raphatex/ESP-32-ruler/Arduino programs/esp32_OS/icons.h

/*
 * https://javl.github.io/image2cpp/
 */
// 'icons', 42x42px
const unsigned char icons[][252] PROGMEM = {
  { // tetris
  0x1f, 0xff, 0xff, 0xff, 0xfe, 0x00, 0x3f, 0xff, 0xff, 0xff, 0xff, 0x00, 0x70, 0x00, 0x00, 0x00, 
  0x03, 0x80, 0xe0, 0x00, 0x00, 0x00, 0x01, 0xc0, 0xc0, 0x00, 0x00, 0x00, 0x00, 0xc0, 0xc0, 0x00, 
  0x00, 0x00, 0x00, 0xc0, 0xc1, 0xff, 0xff, 0xff, 0xe0, 0xc0, 0xc1, 0x00, 0x80, 0x40, 0x20, 0xc0, 
  0xc1, 0x7e, 0xbf, 0x5f, 0xa0, 0xc0, 0xc1, 0x7e, 0xbf, 0x5f, 0xa0, 0xc0, 0xc1, 0x7e, 0xbf, 0x5f, 
  0xa0, 0xc0, 0xc1, 0x7e, 0xbf, 0x5f, 0xa0, 0xc0, 0xc1, 0x7e, 0xbf, 0x5f, 0xa0, 0xc0, 0xc1, 0x7e, 
  0xbf, 0x5f, 0xa0, 0xc0, 0xc1, 0x00, 0x80, 0x40, 0x20, 0xc0, 0xc1, 0xff, 0xff, 0xff, 0xe0, 0xc0, 
  0xc0, 0x00, 0x80, 0x40, 0x00, 0xc0, 0xc0, 0x00, 0xbf, 0x40, 0x00, 0xc0, 0xc0, 0x00, 0xbf, 0x40, 
  0x00, 0xc0, 0xc0, 0x00, 0xbf, 0x40, 0x00, 0xc0, 0xc0, 0x00, 0xbf, 0x40, 0x00, 0xc0, 0xc0, 0x00, 
  0xbf, 0x40, 0x00, 0xc0, 0xc0, 0x00, 0xbf, 0x40, 0x00, 0xc0, 0xc0, 0x00, 0x80, 0x40, 0x00, 0xc0, 
  0xc0, 0x00, 0xff, 0xc0, 0x00, 0xc0, 0xc0, 0x00, 0x00, 0x00, 0x00, 0xc0, 0xc0, 0x00, 0x00, 0x00, 
  0x00, 0xc0, 0xc0, 0x00, 0x00, 0x00, 0x00, 0xc0, 0xc0, 0x00, 0x00, 0x00, 0x00, 0xc0, 0xc3, 0xef, 
  0x7d, 0xe2, 0xf0, 0xc0, 0xc0, 0x88, 0x11, 0x10, 0x80, 0xc0, 0xc0, 0x88, 0x11, 0x12, 0x80, 0xc0, 
  0xc0, 0x8e, 0x11, 0xe2, 0xf0, 0xc0, 0xc0, 0x88, 0x11, 0x42, 0x10, 0xc0, 0xc0, 0x88, 0x11, 0x22, 
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
	0x20, 0xc0, 0xc0, 0xff, 0xe1, 0xff, 0xc0, 0xc0, 0xc0, 0x00, 0x00, 0x00, 0x00, 0xc0, 0xc0, 0x00, 
	0x00, 0x00, 0x00, 0xc0, 0xe0, 0x00, 0x00, 0x00, 0x01, 0xc0, 0x70, 0x00, 0x00, 0x00, 0x03, 0x80, 
	0x3f, 0xff, 0xff, 0xff, 0xff, 0x00, 0x1f, 0xff, 0xff, 0xff, 0xfe, 0x00
  }
};
